dnhutchins/ETC_Express_Reverse_Eng/internal-photos/CONTROL_BACK_2.jpg

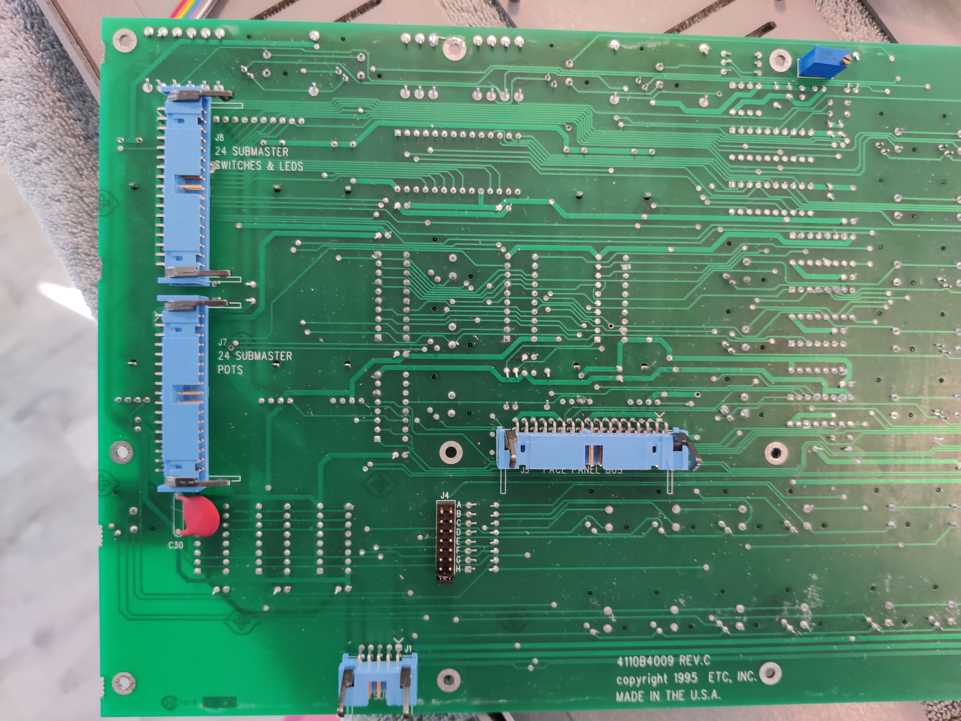
internal-photos/CONTROL_BACK_2.jpg
