dnhutchins/ETC_Express_Reverse_Eng/internal-photos/CONTROL_BACK_3.jpg

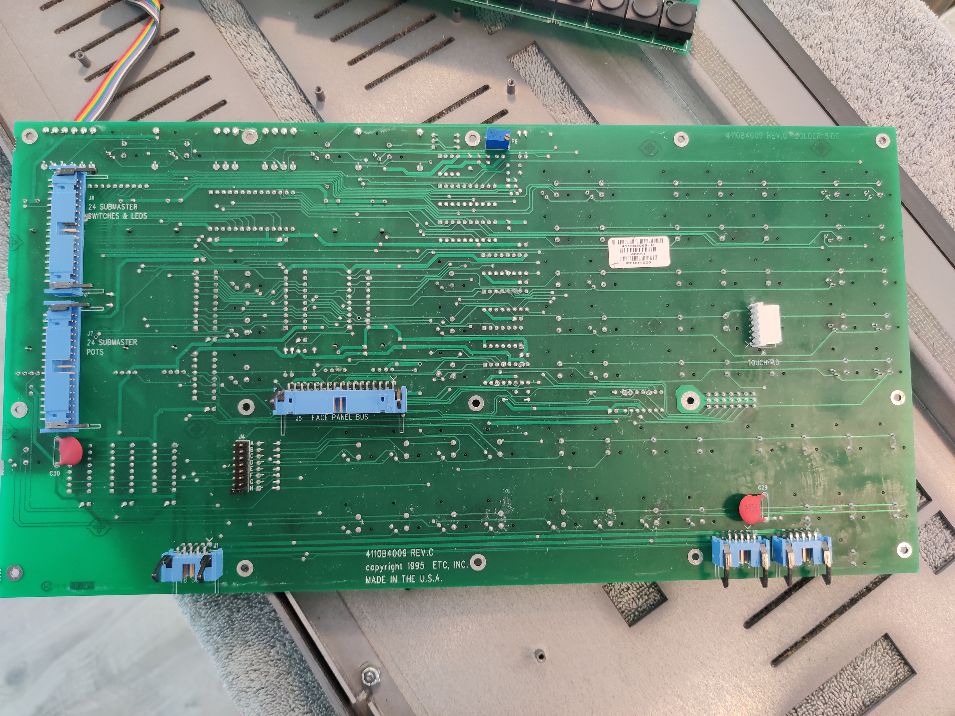
internal-photos/CONTROL_BACK_3.jpg
