dnhutchins/ETC_Express_Reverse_Eng/internal-photos/CONTROL_BACK_4.jpg

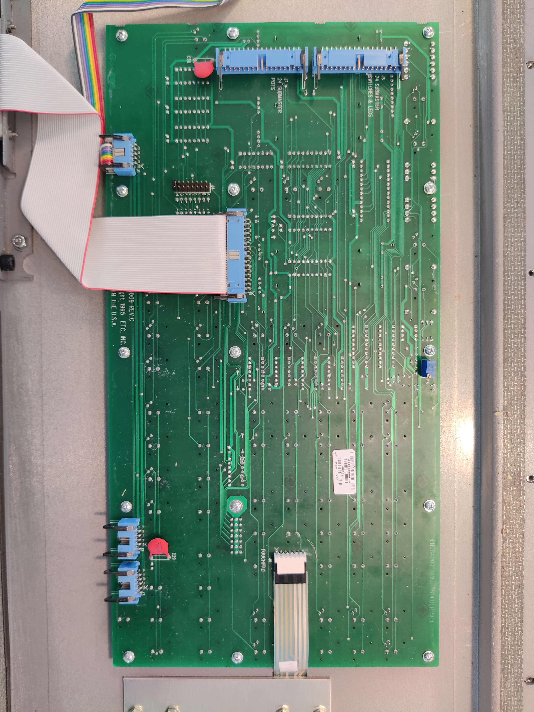
internal-photos/CONTROL_BACK_4.jpg
