dnhutchins/ETC_Express_Reverse_Eng/internal-photos/CONTROL_BACK_5.jpg

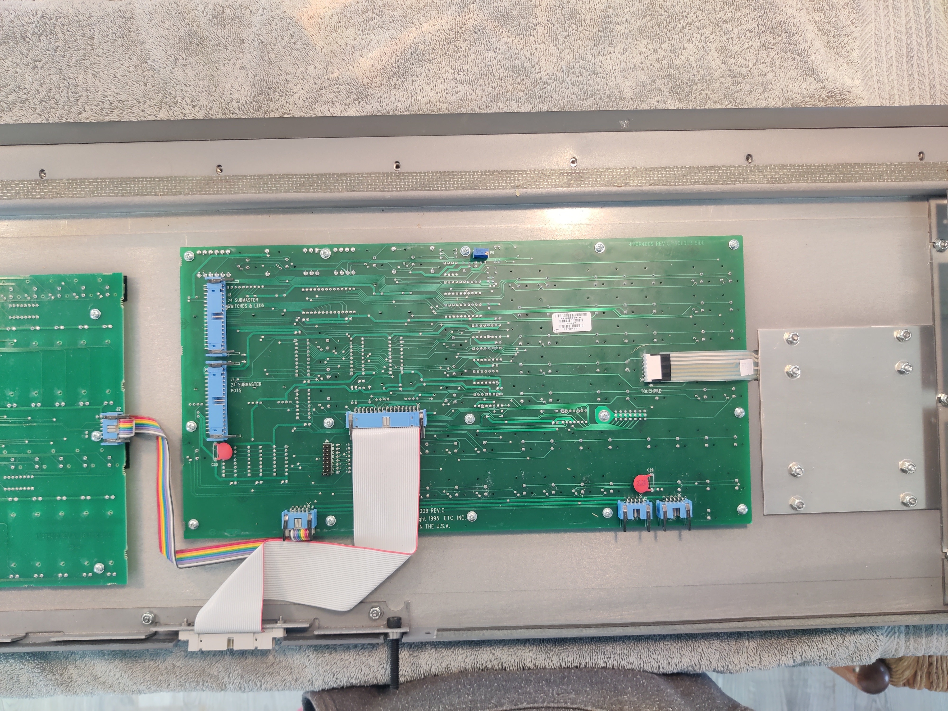
internal-photos/CONTROL_BACK_5.jpg
