dnhutchins/ETC_Express_Reverse_Eng/internal-photos/CONTROL_FRONT_6.jpg

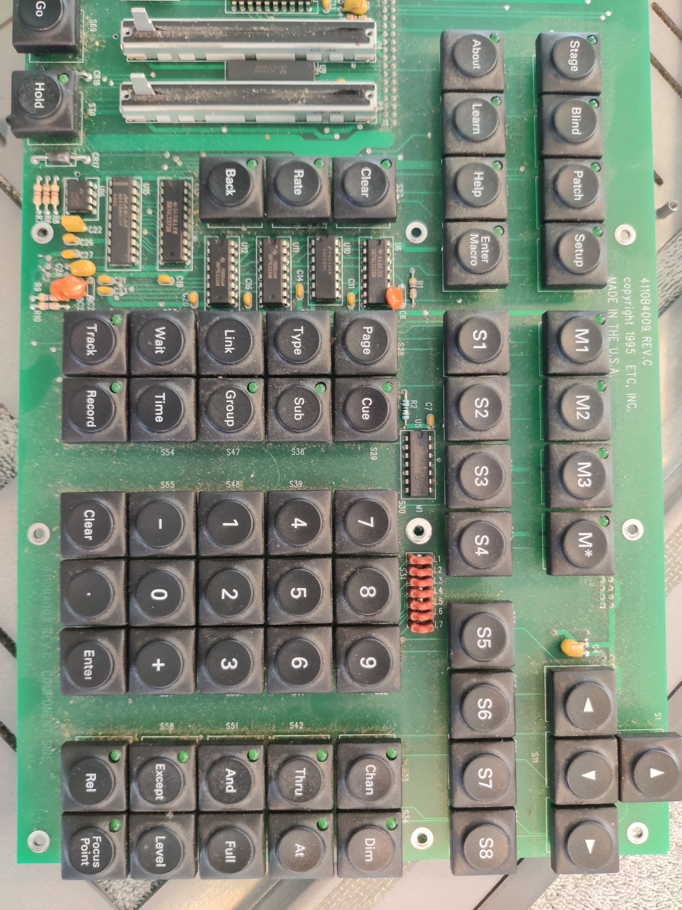
internal-photos/CONTROL_FRONT_6.jpg
