dnhutchins/ETC_Express_Reverse_Eng/internal-photos/CONTROL_FRONT_7.jpg

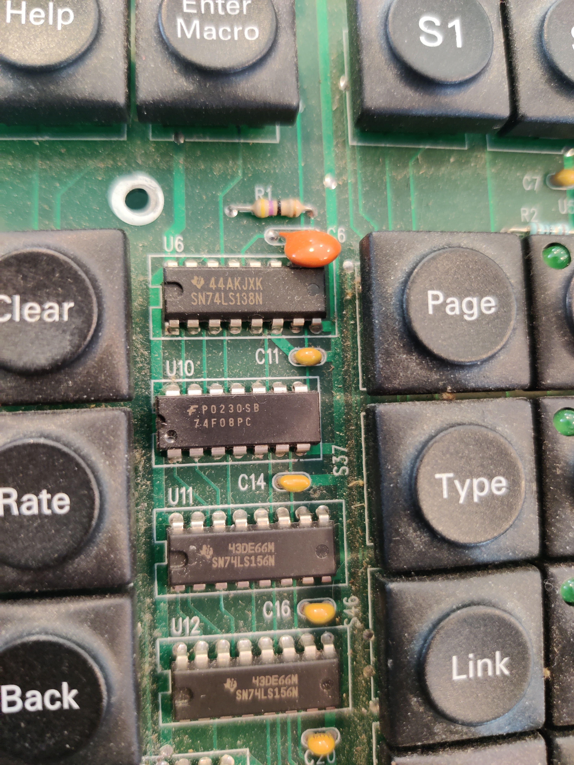
internal-photos/CONTROL_FRONT_7.jpg
