dnhutchins/ETC_Express_Reverse_Eng/internal-photos/CONTROL_FRONT_10.jpg

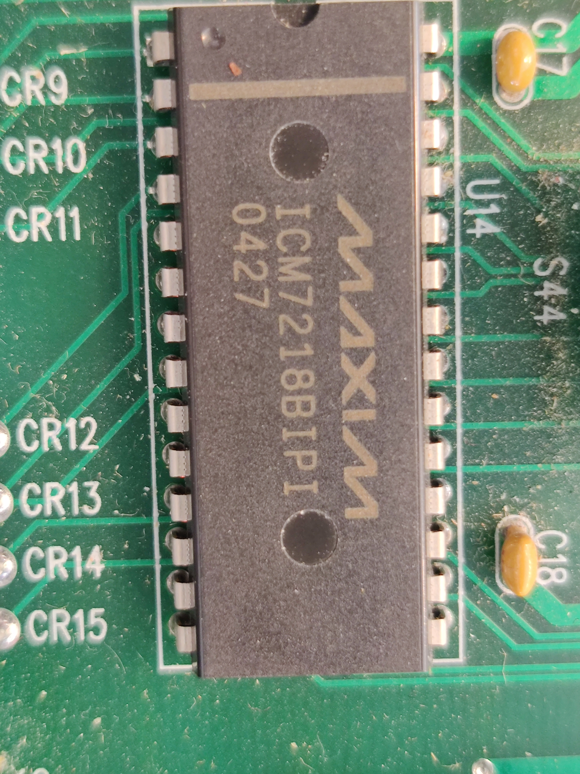
internal-photos/CONTROL_FRONT_10.jpg
