dnhutchins/ETC_Express_Reverse_Eng/internal-photos/CONTROL_SURFACE_INTERFACE.jpg

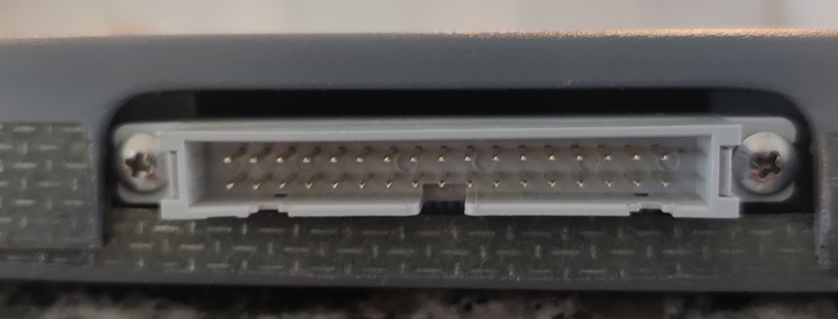
internal-photos/CONTROL_SURFACE_INTERFACE.jpg
