dnhutchins/ETC_Express_Reverse_Eng/internal-photos/CPU_BOARD_1.jpg

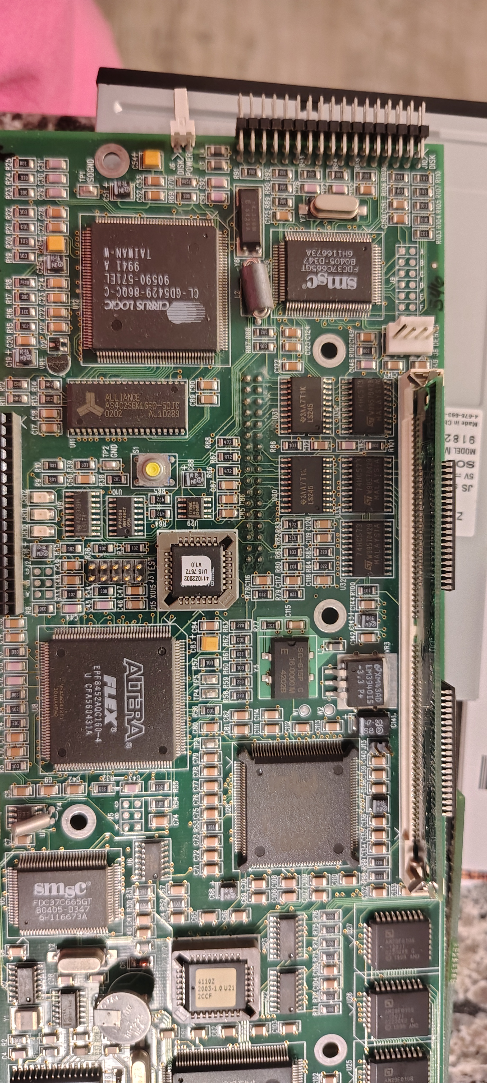
internal-photos/CPU_BOARD_1.jpg
