dnhutchins/ETC_Express_Reverse_Eng/internal-photos/FADER_BACK_1.jpg

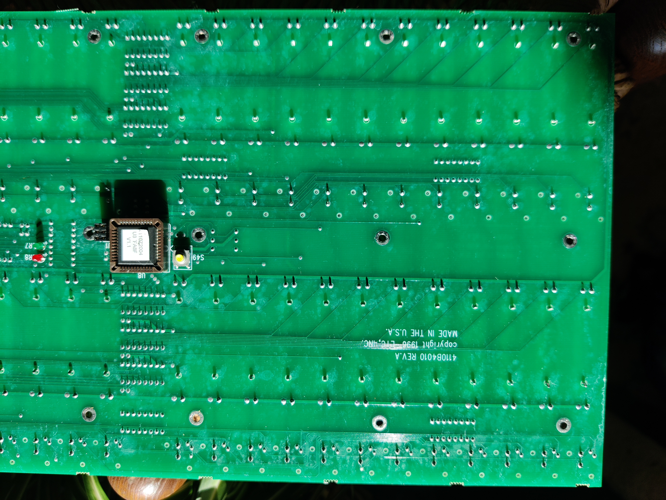
internal-photos/FADER_BACK_1.jpg
