dnhutchins/ETC_Express_Reverse_Eng/internal-photos/FADER_BACK_2.jpg

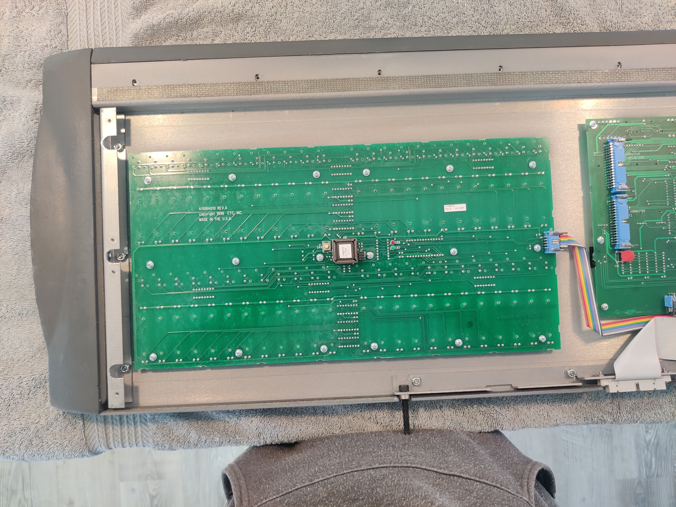
internal-photos/FADER_BACK_2.jpg
