dnhutchins/ETC_Express_Reverse_Eng/internal-photos/FADER_BACK_4.jpg

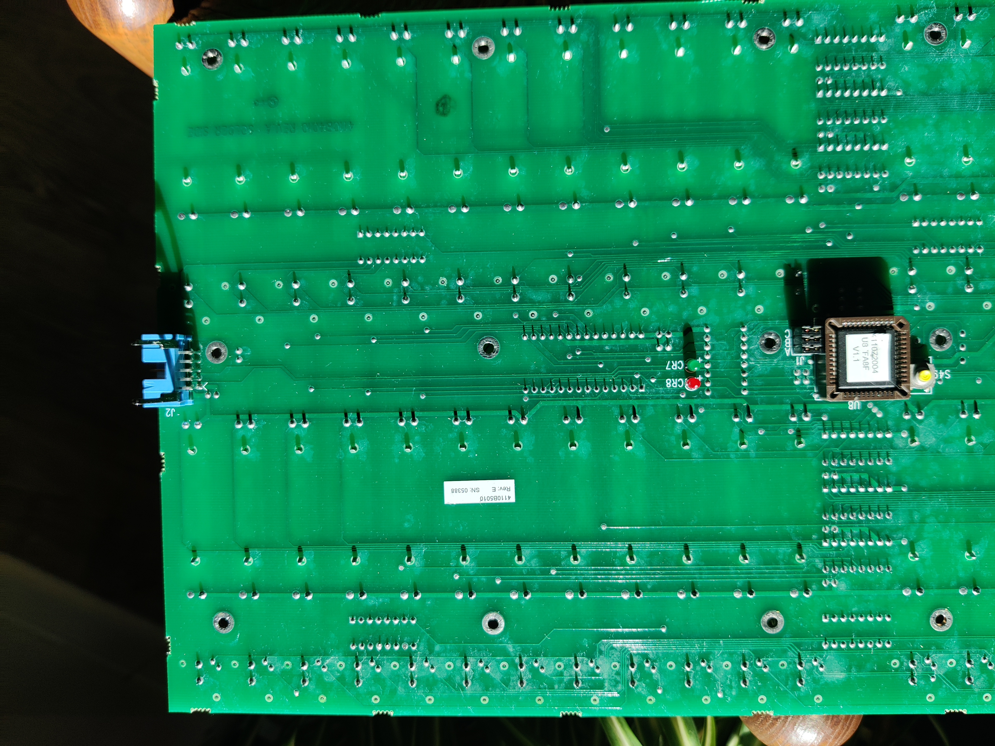
internal-photos/FADER_BACK_4.jpg
