dnhutchins/ETC_Express_Reverse_Eng/internal-photos/FADER_BACK_5.jpg

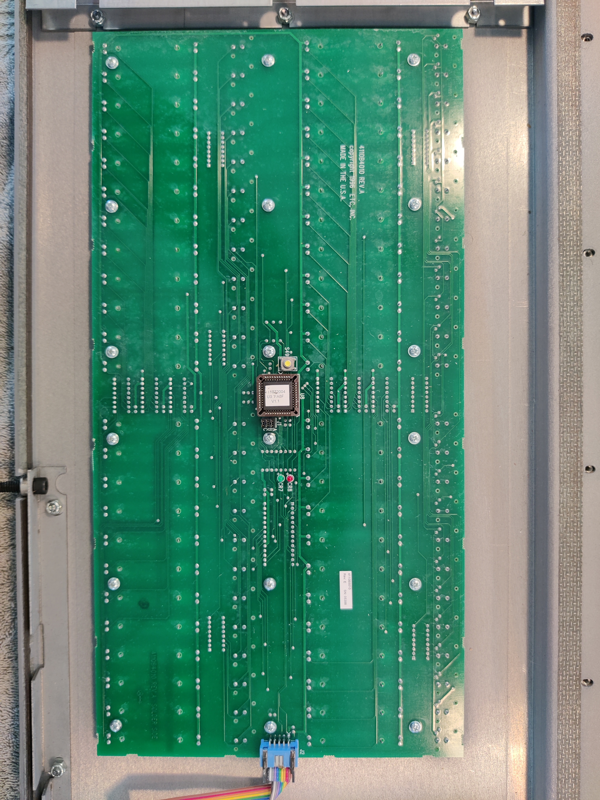
internal-photos/FADER_BACK_5.jpg
