dnhutchins/ETC_Express_Reverse_Eng/internal-photos/FADER_FRONT_4.jpg

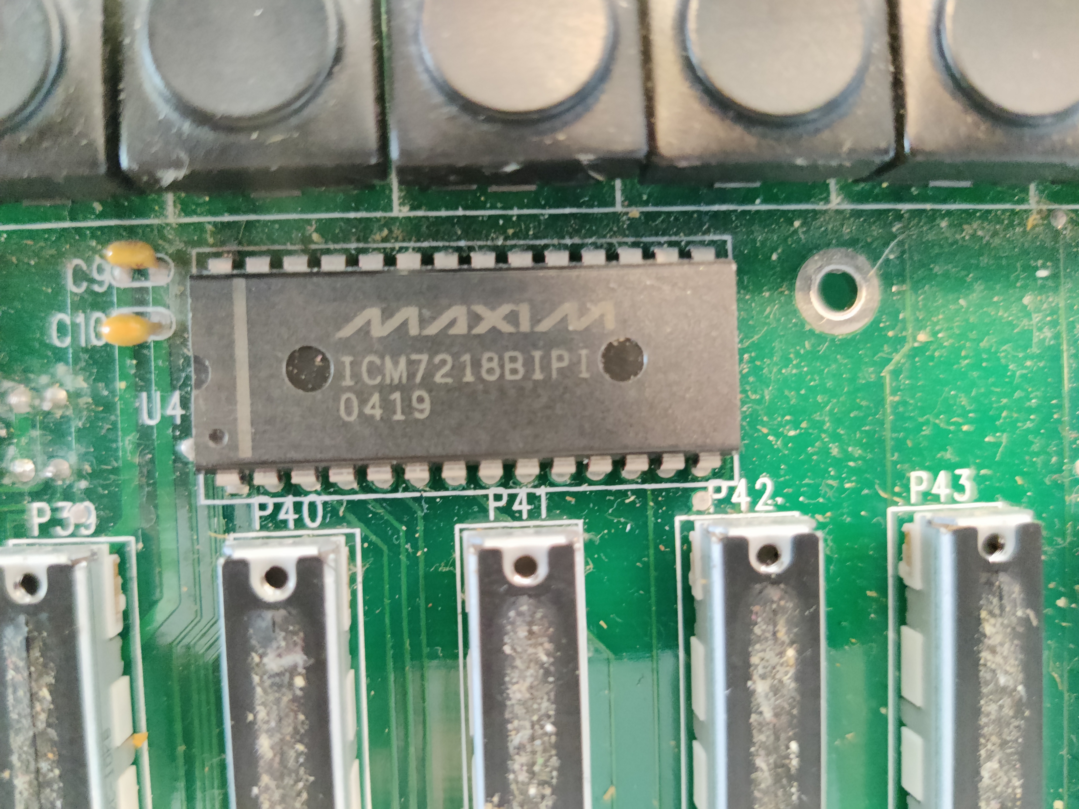
internal-photos/FADER_FRONT_4.jpg
