dnhutchins/ETC_Express_Reverse_Eng/internal-photos/ASSEMBLED_BACK.jpg

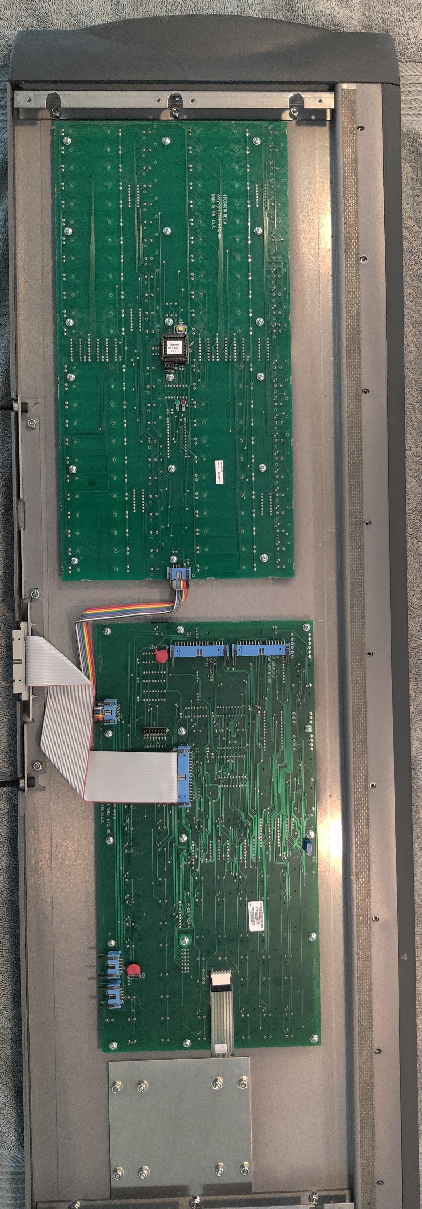
internal-photos/ASSEMBLED_BACK.jpg
